Hasona57/Smart-Road/3D/led-3mm-green.snapshot.3/Renderings/led 3mm green.jpg

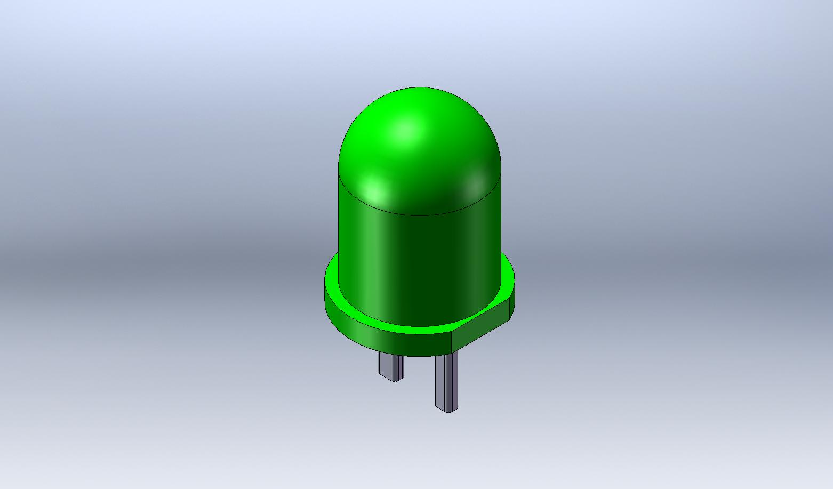
3D/led-3mm-green.snapshot.3/Renderings/led 3mm green.jpg
