Hasona57/Smart-Road/3D/led-3mm-green.snapshot.3/Renderings/untitled.340.jpg

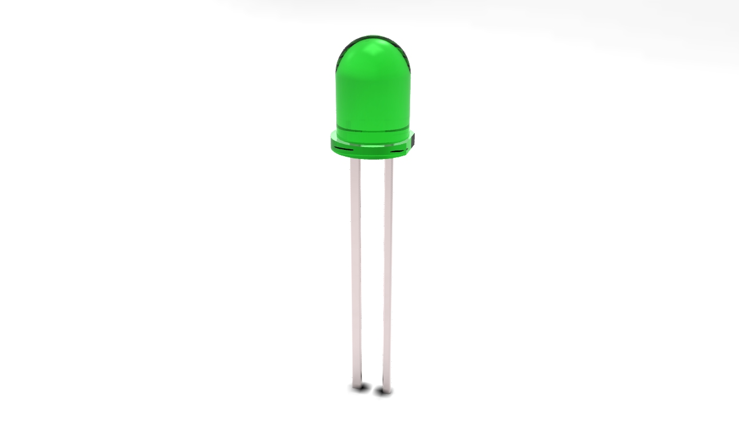
3D/led-3mm-green.snapshot.3/Renderings/untitled.340.jpg
