Hasona57/Smart-Road/3D/Traffic light module 3D/Traffic lights LED Module.jpg

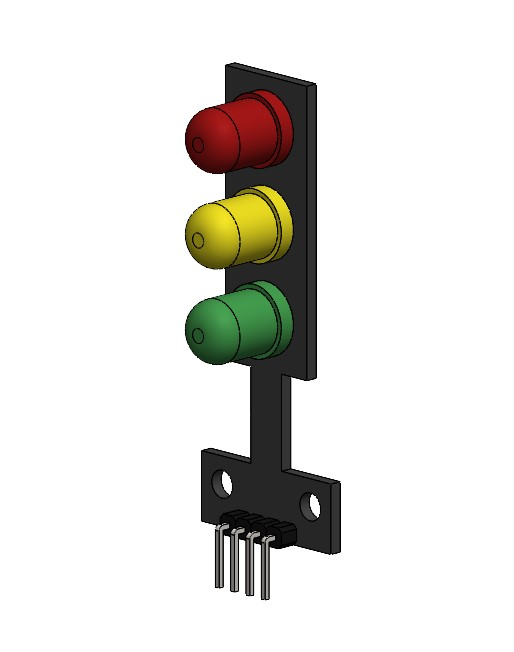
3D/Traffic light module 3D/Traffic lights LED Module.jpg
