Hasona57/Smart-Road/AI/assets/road3.jpg

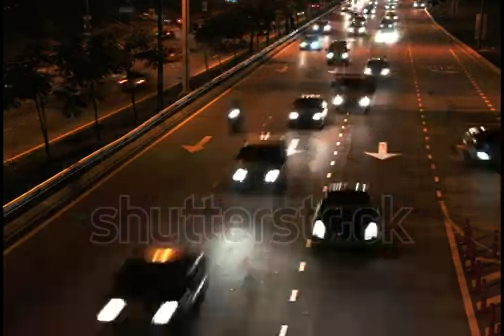
AI/assets/road3.jpg
