Hasona57/Smart-Road/AI/assets/road4.jpg

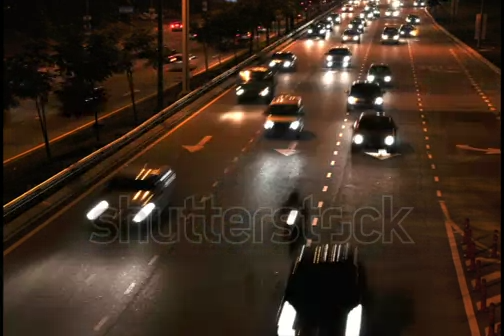
AI/assets/road4.jpg
