Hasona57/Smart-Road/AI/assets/road6.jpg

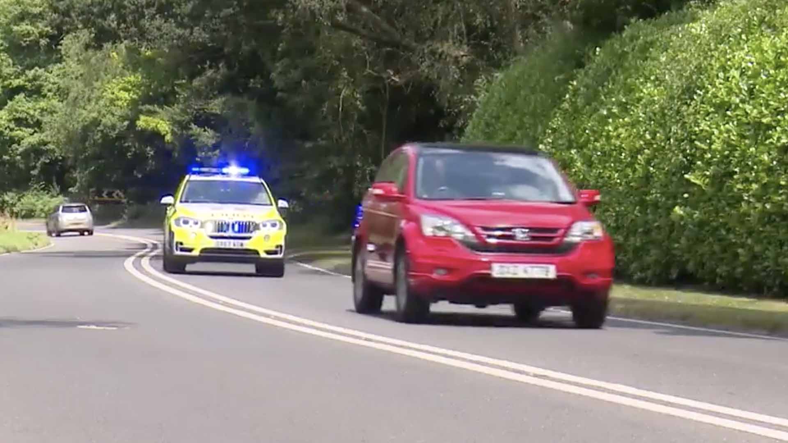
AI/assets/road6.jpg
