Hasona57/Smart-Road/AI/runs/detect/train/confusion_matrix.png

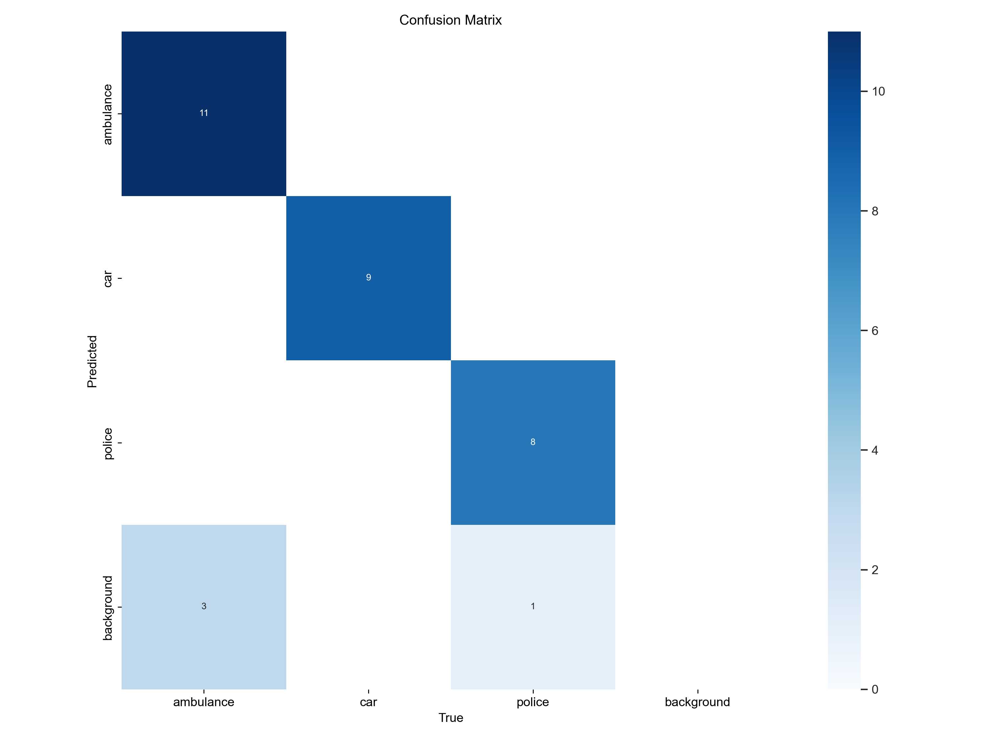
AI/runs/detect/train/confusion_matrix.png
