Hasona57/Smart-Road/AI/runs/detect/train/F1_curve.png

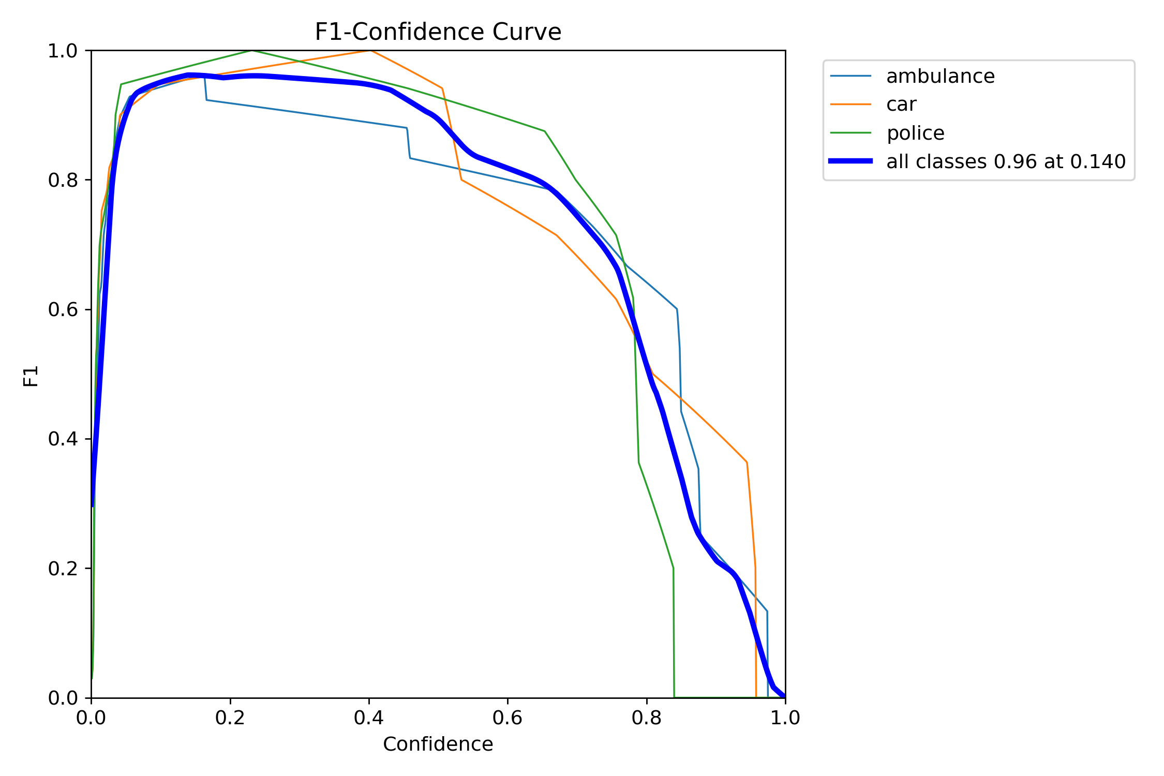
AI/runs/detect/train/F1_curve.png
