Hasona57/Smart-Road/AI/runs/detect/train/labels.jpg

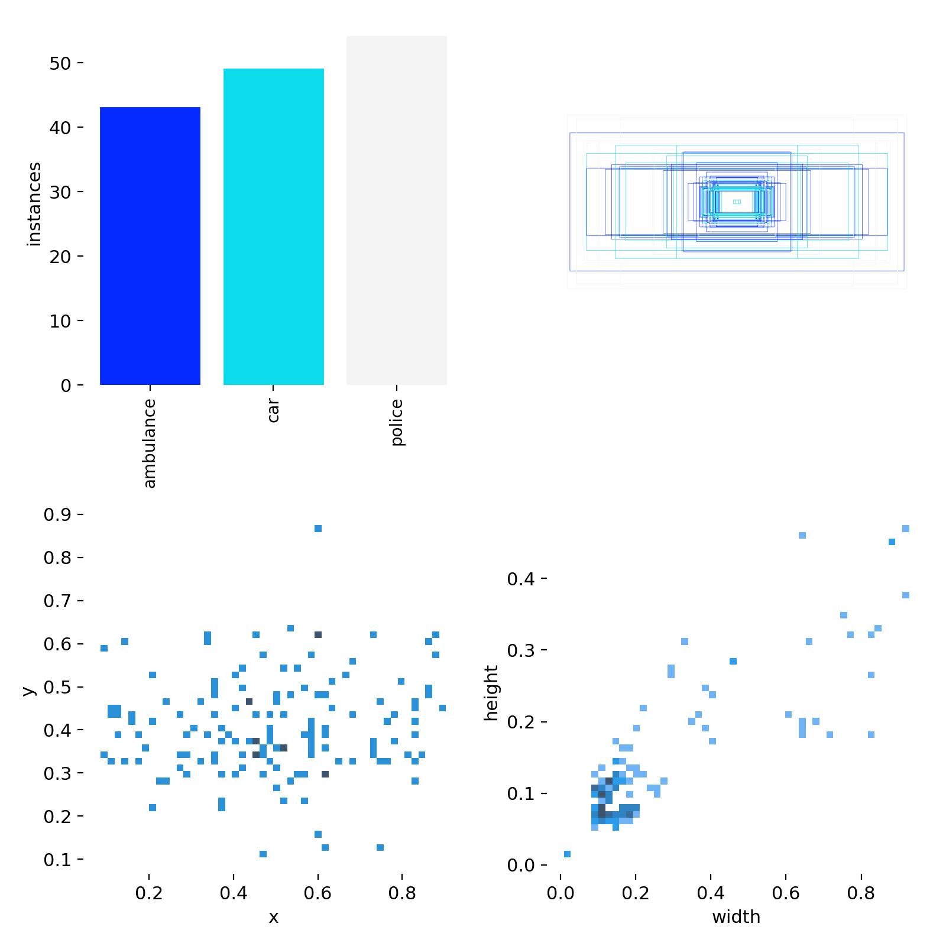
AI/runs/detect/train/labels.jpg
