Hasona57/Smart-Road/AI/runs/detect/train/labels_correlogram.jpg

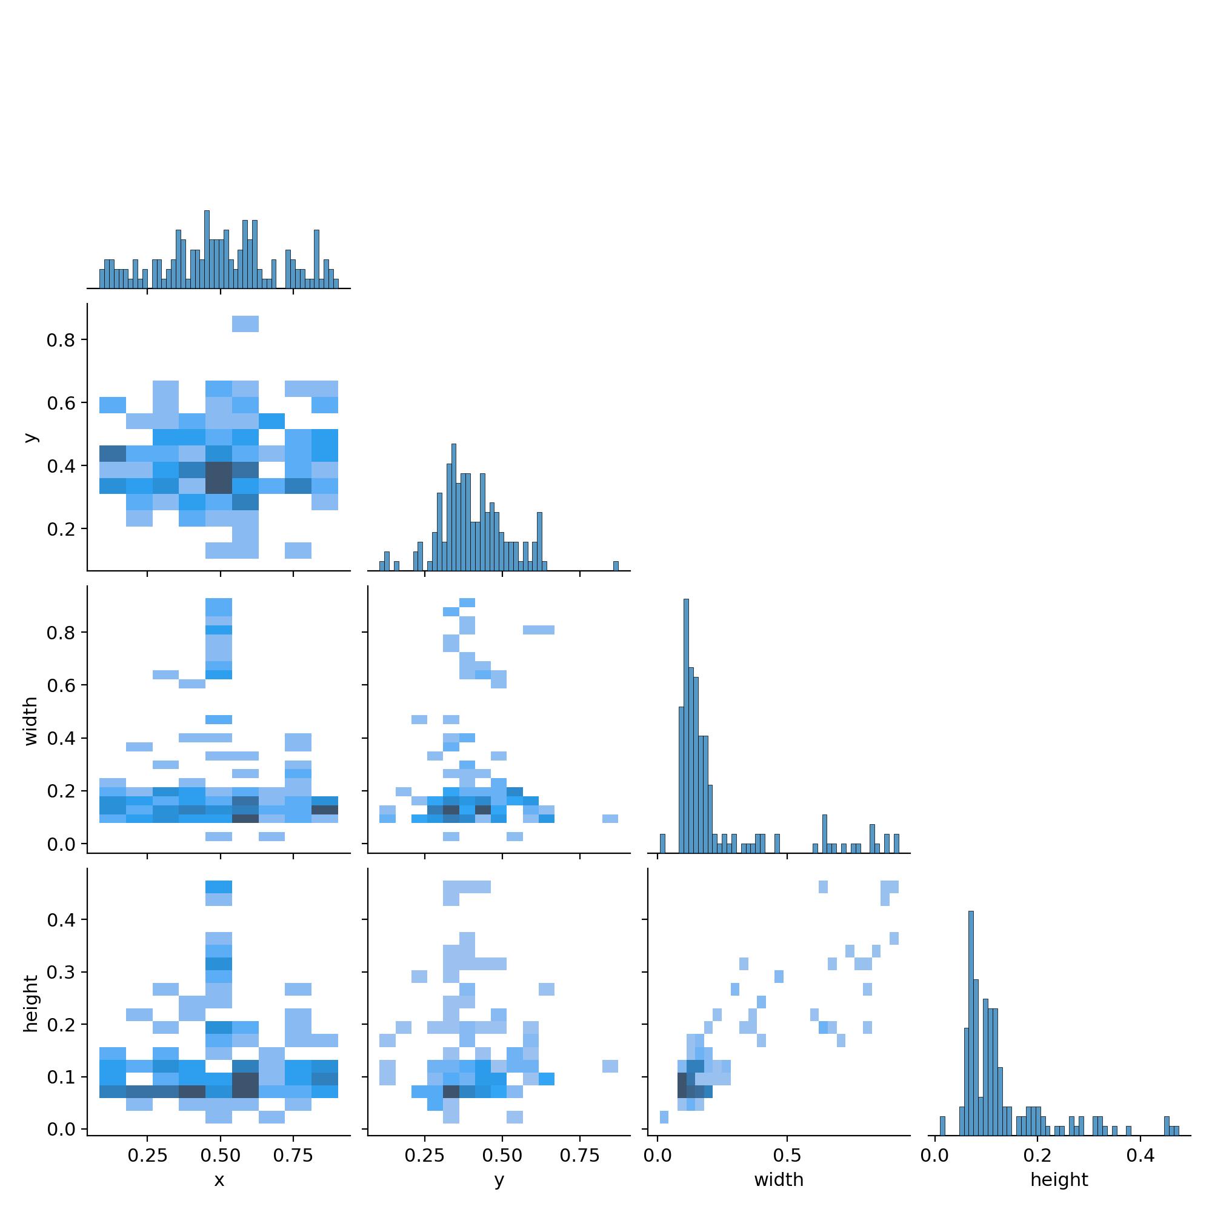
AI/runs/detect/train/labels_correlogram.jpg
