Hasona57/Smart-Road/AI/runs/detect/train/P_curve.png

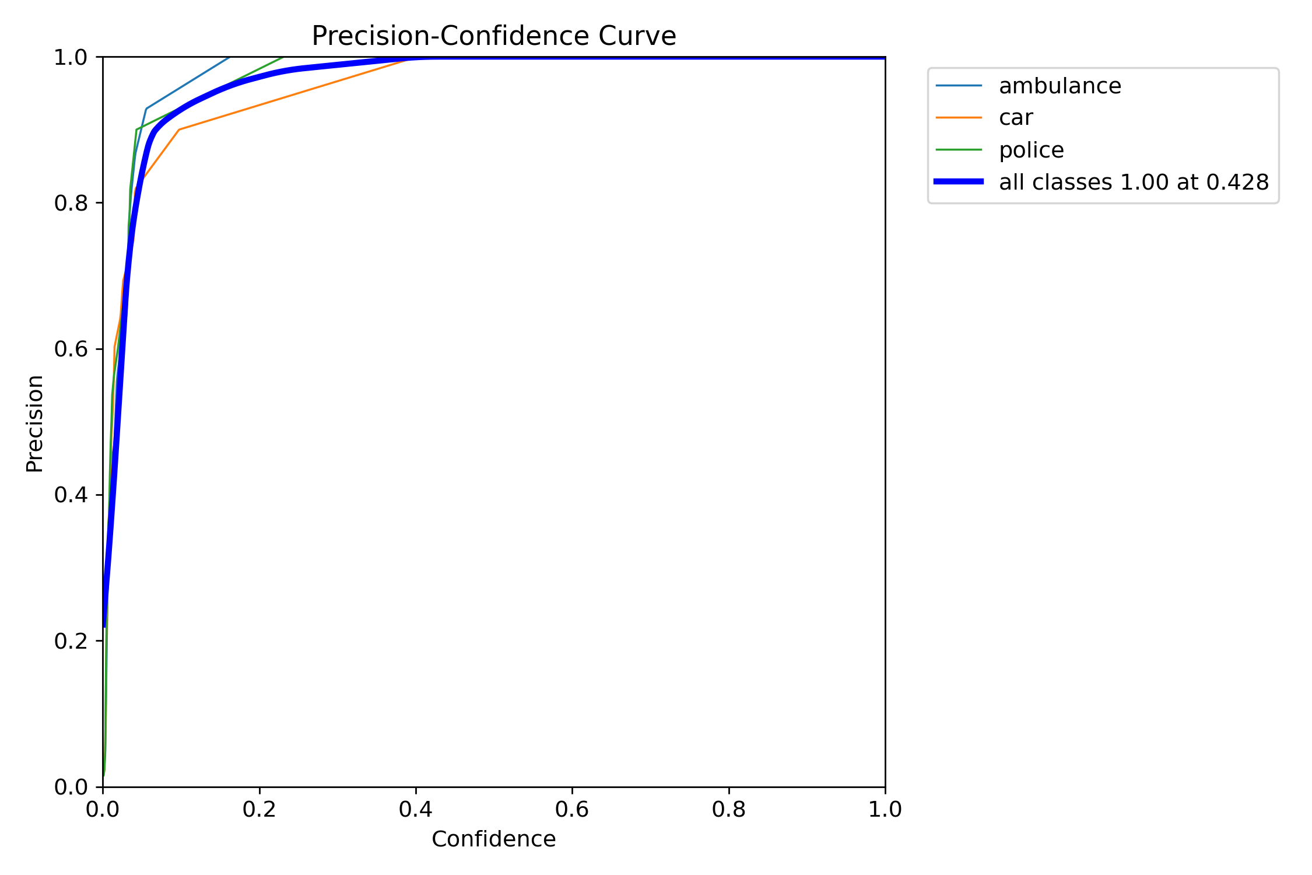
AI/runs/detect/train/P_curve.png
