Hasona57/Smart-Road/AI/runs/detect/train/PR_curve.png

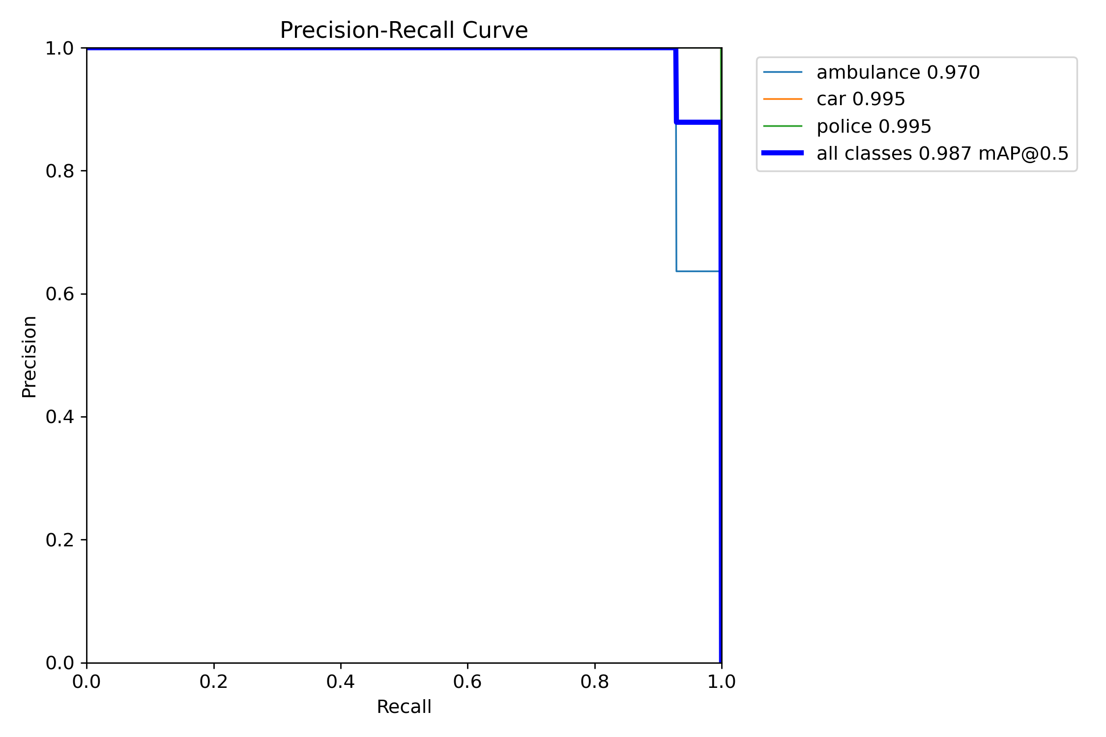
AI/runs/detect/train/PR_curve.png
