Hasona57/Smart-Road/AI/runs/detect/train/train_batch0.jpg

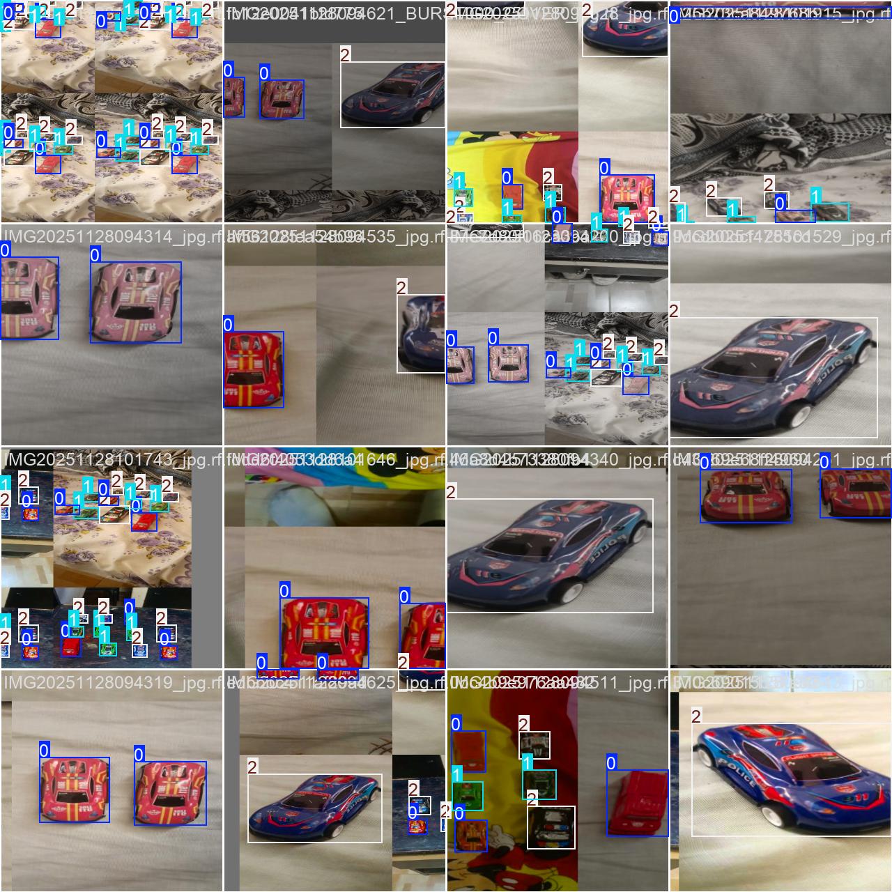
AI/runs/detect/train/train_batch0.jpg
