Hasona57/Smart-Road/AI/runs/detect/train/train_batch1.jpg

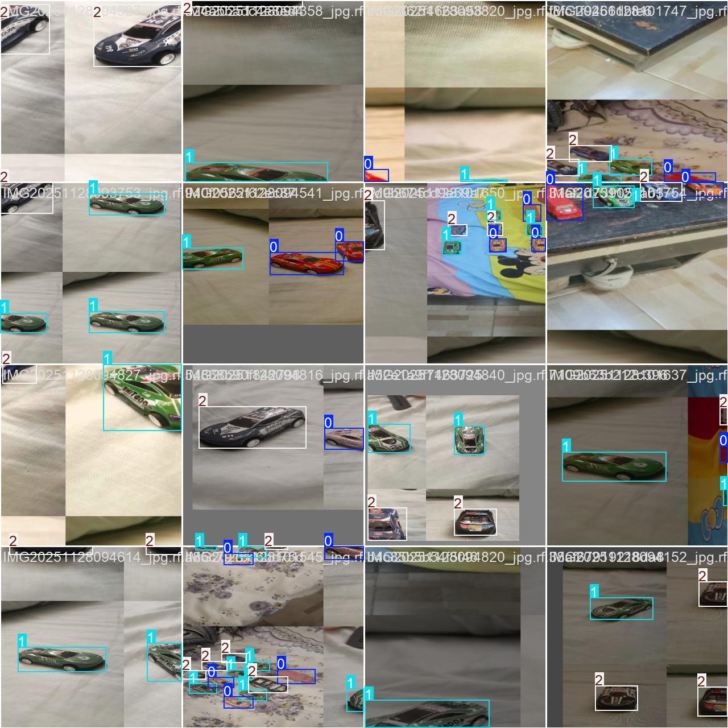
AI/runs/detect/train/train_batch1.jpg
