Hasona57/Smart-Road/AI/runs/detect/train/train_batch2.jpg

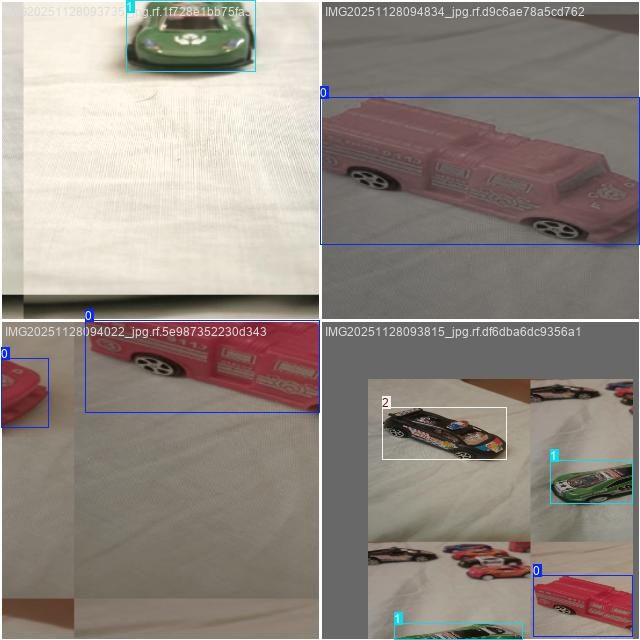
AI/runs/detect/train/train_batch2.jpg
