Hasona57/Smart-Road/AI/runs/detect/train/train_batch120.jpg

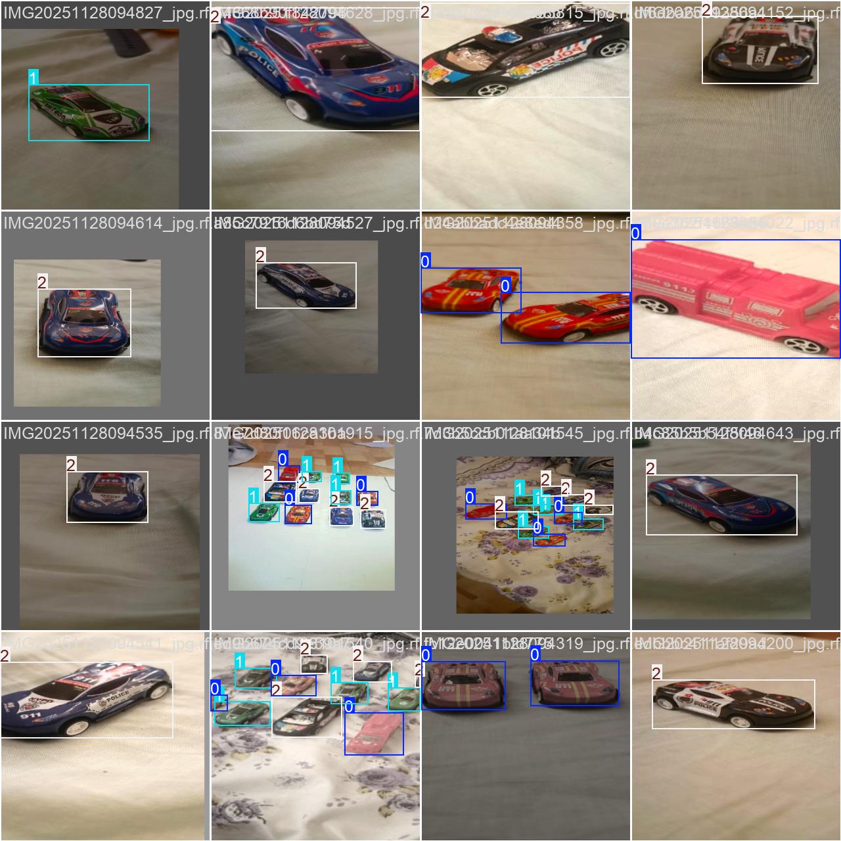
AI/runs/detect/train/train_batch120.jpg
