Hasona57/Smart-Road/AI/runs/detect/train/train_batch121.jpg

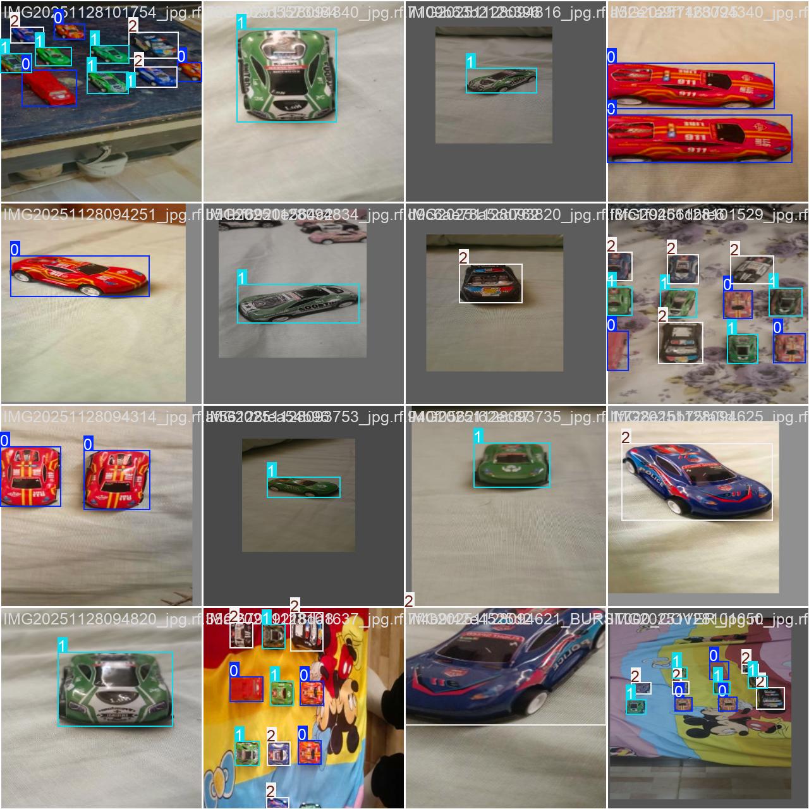
AI/runs/detect/train/train_batch121.jpg
