Hasona57/Smart-Road/AI/runs/detect/train/train_batch122.jpg

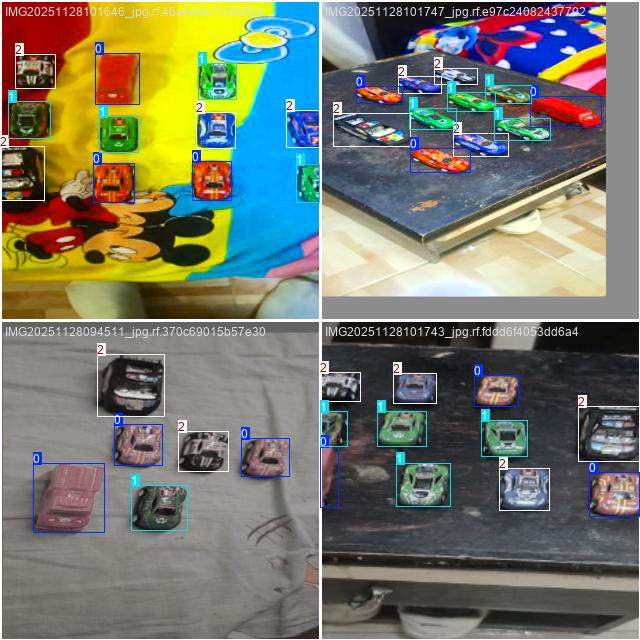
AI/runs/detect/train/train_batch122.jpg
