Hasona57/Smart-Road/AI/runs/detect/train/val_batch0_labels.jpg

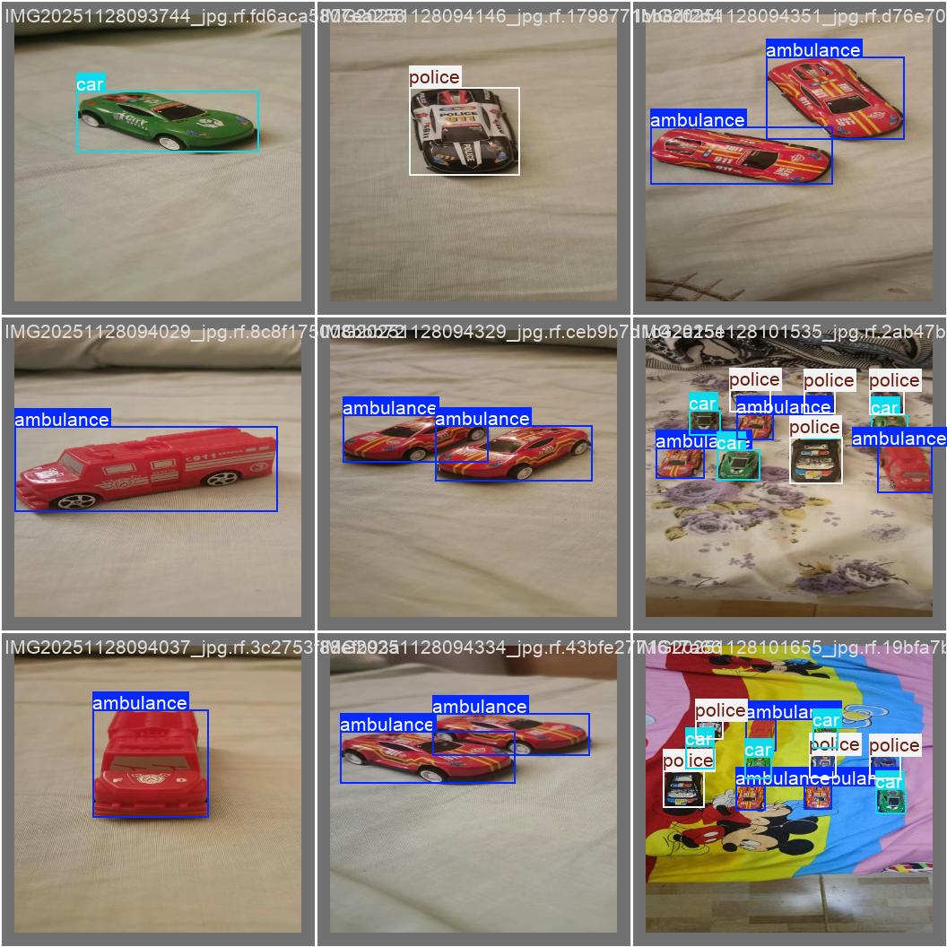
AI/runs/detect/train/val_batch0_labels.jpg
