Hasona57/Smart-Road/AI/runs/detect/train/val_batch0_pred.jpg

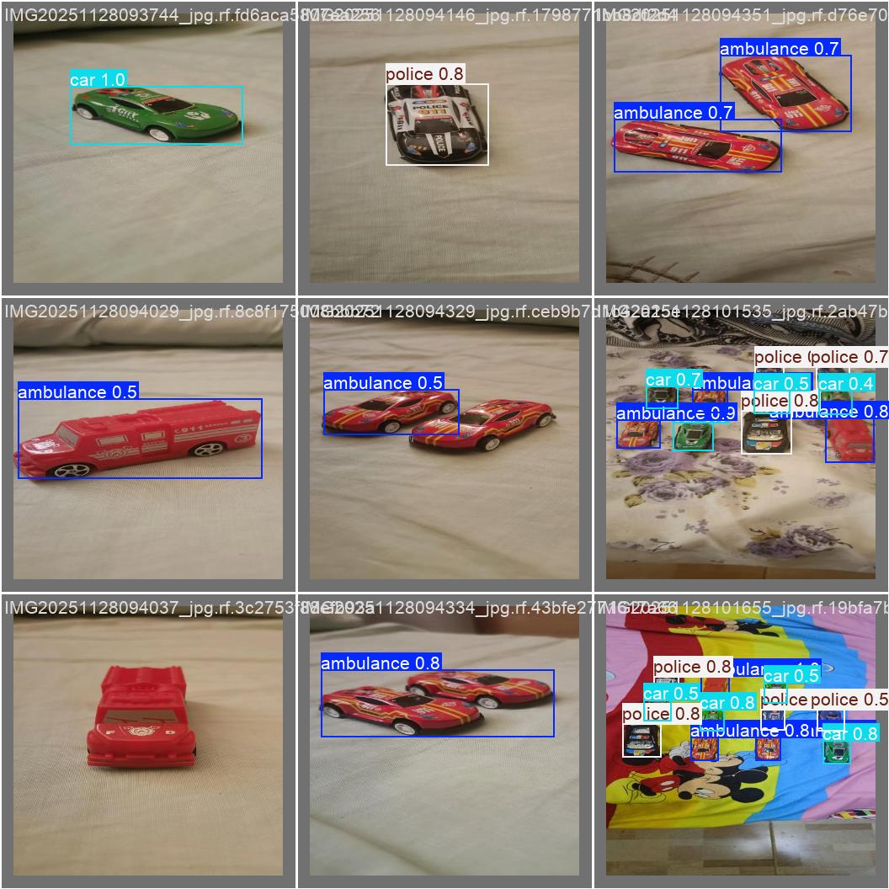
AI/runs/detect/train/val_batch0_pred.jpg
