Hasona57/Smart-Road/Code/Labels/Hassan/IMG20251128093744.jpg

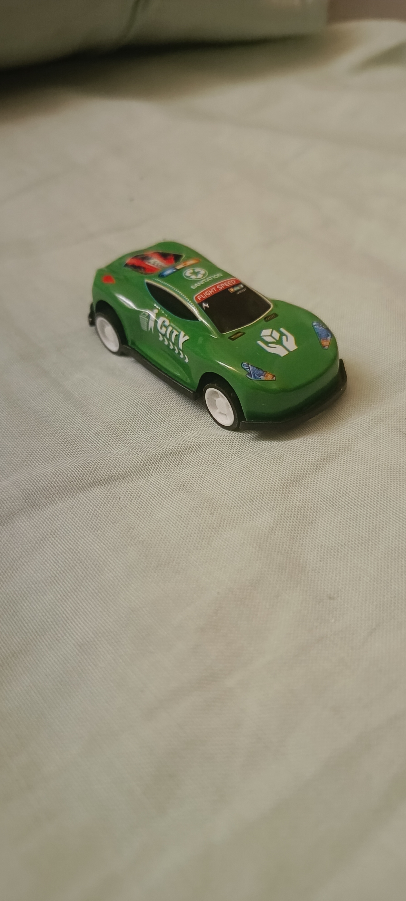
Code/Labels/Hassan/IMG20251128093744.jpg
