Hasona57/Smart-Road/Code/Labels/Hassan/IMG20251128093753.jpg

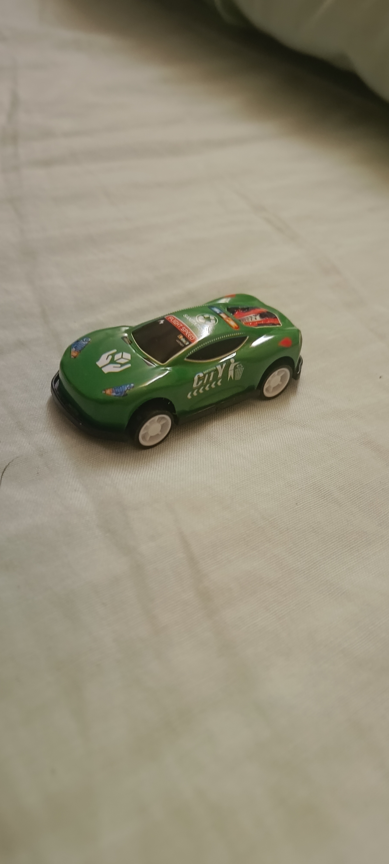
Code/Labels/Hassan/IMG20251128093753.jpg
