Hasona57/Smart-Road/Code/Labels/Hassan/IMG20251128093759.jpg

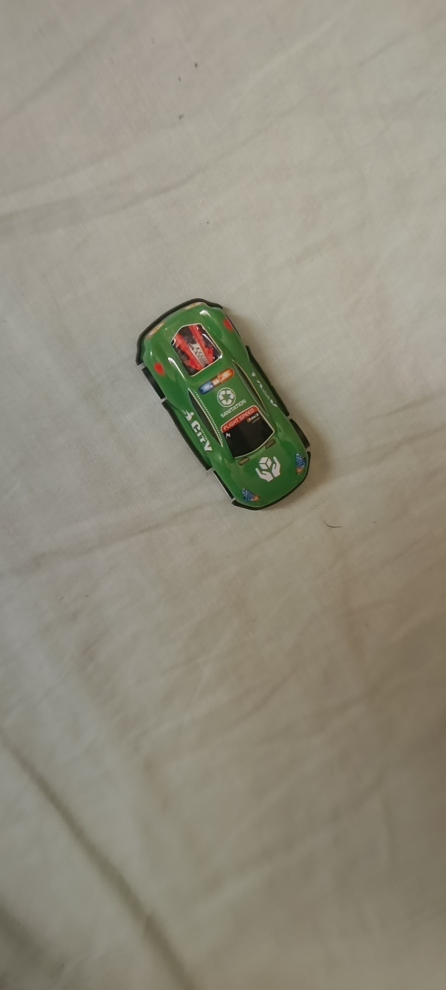
Code/Labels/Hassan/IMG20251128093759.jpg
