Hasona57/Smart-Road/Code/Labels/Hassan/IMG20251128093808.jpg

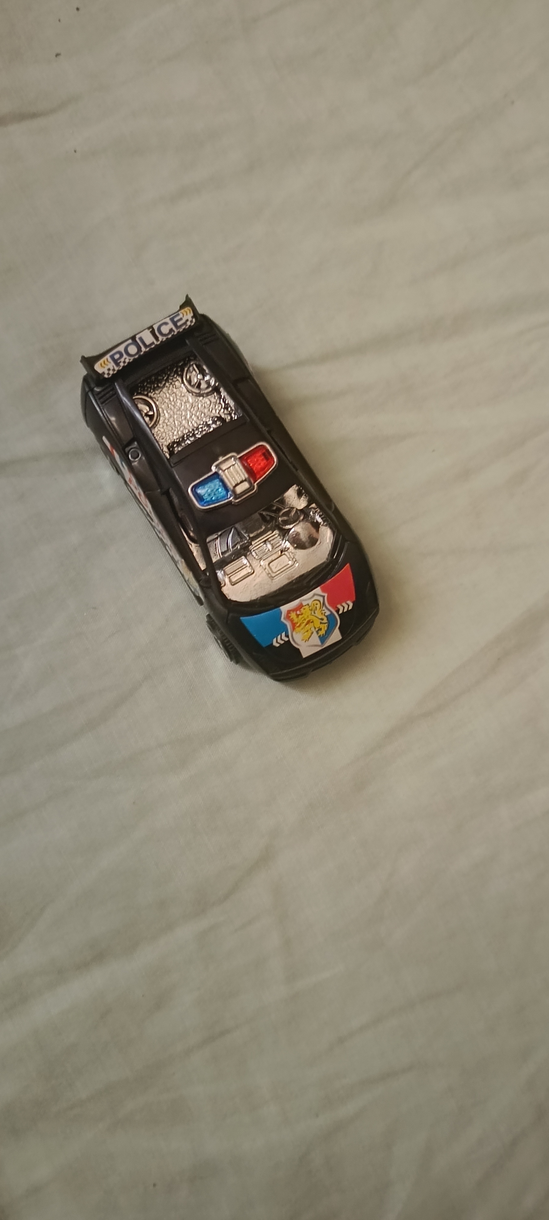
Code/Labels/Hassan/IMG20251128093808.jpg
