Hasona57/Smart-Road/Code/Labels/Hassan/IMG20251128093820.jpg

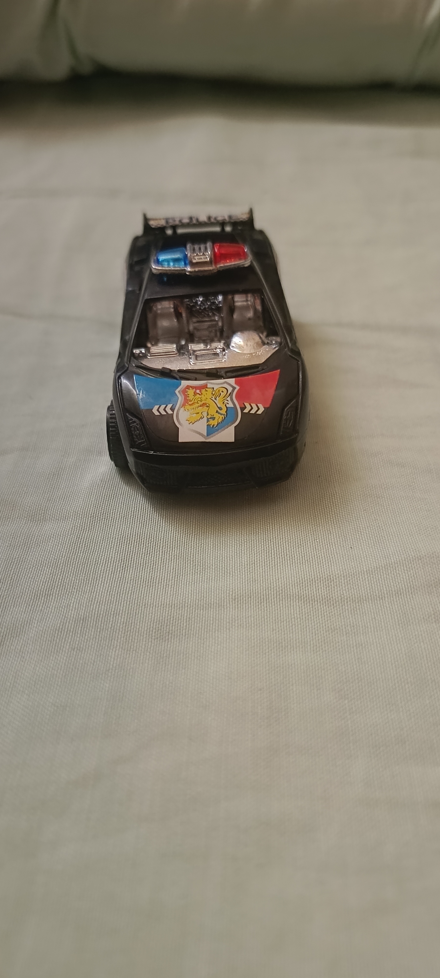
Code/Labels/Hassan/IMG20251128093820.jpg
