Hasona57/Smart-Road/Code/Labels/Hassan/IMG20251128093831.jpg

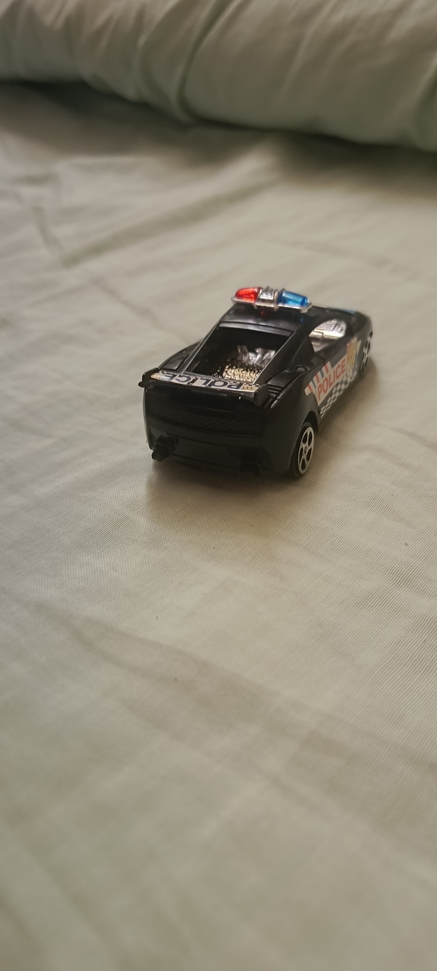
Code/Labels/Hassan/IMG20251128093831.jpg
