Hasona57/Smart-Road/Code/Labels/Hassan/IMG20251128094015.jpg

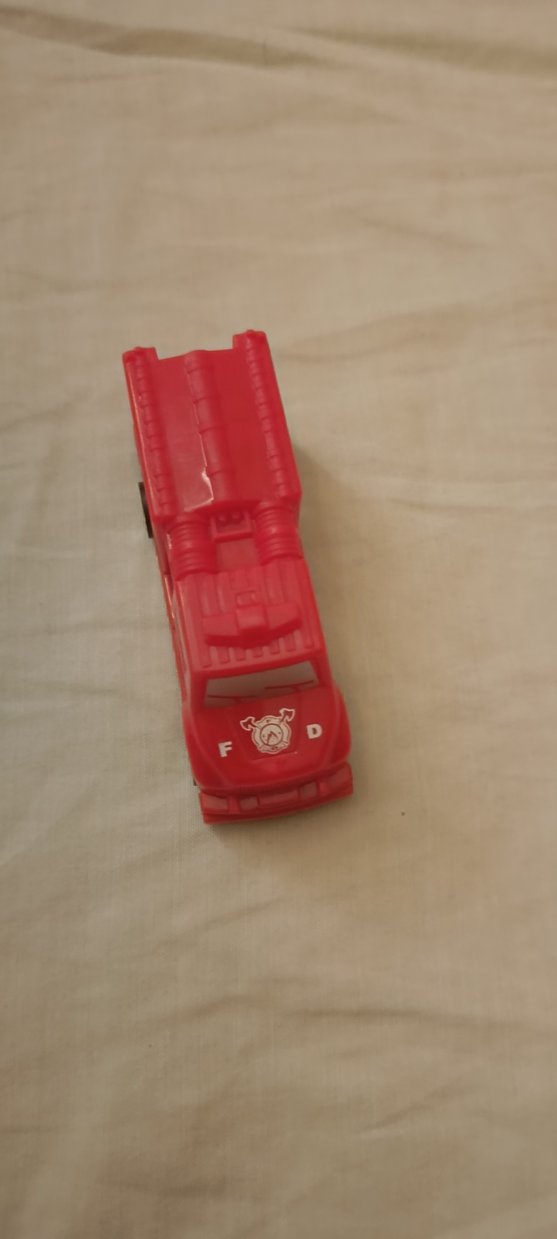
Code/Labels/Hassan/IMG20251128094015.jpg
