Hasona57/Smart-Road/Code/Labels/Hassan/IMG20251128094037.jpg

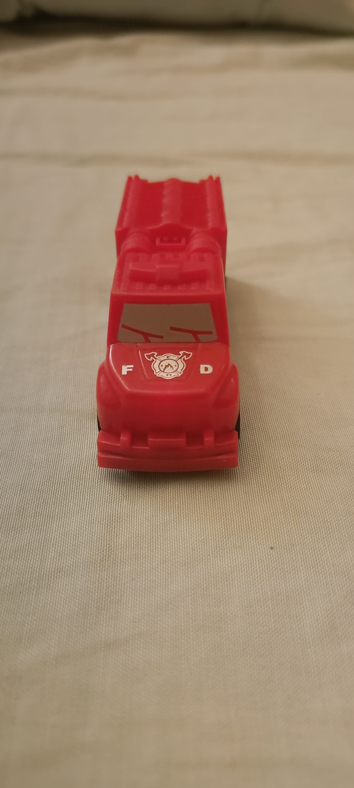
Code/Labels/Hassan/IMG20251128094037.jpg
