Hasona57/Smart-Road/Code/Labels/Hassan/IMG20251128094051.jpg

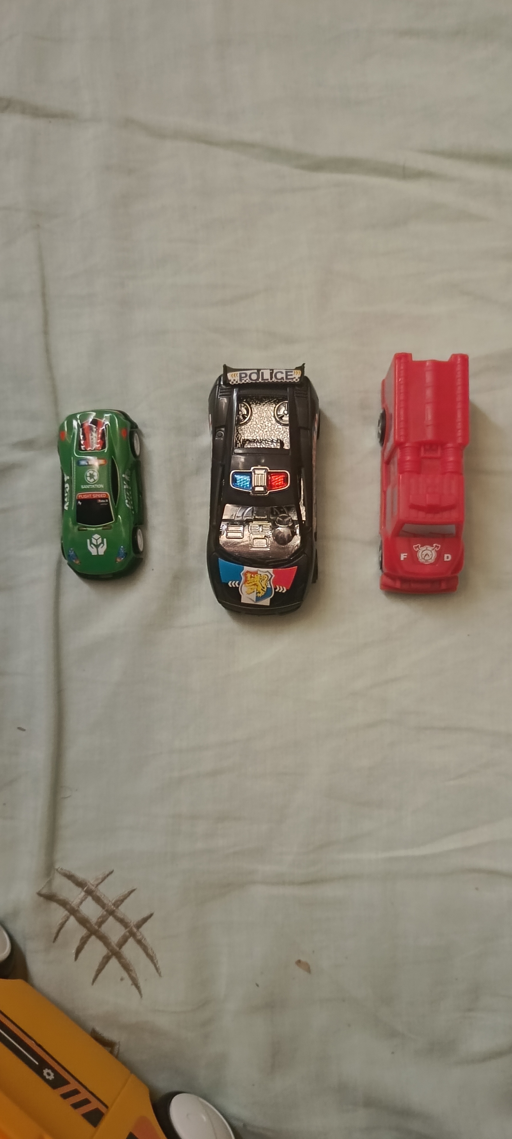
Code/Labels/Hassan/IMG20251128094051.jpg
