Hasona57/Smart-Road/Code/Labels/Hassan/IMG20251128094816.jpg

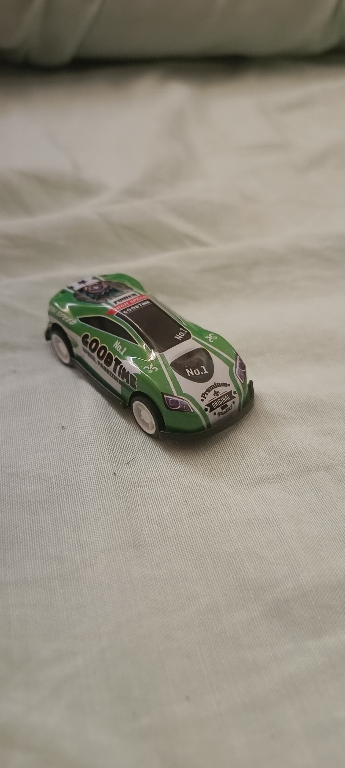
Code/Labels/Hassan/IMG20251128094816.jpg
