Hasona57/Smart-Road/Code/Labels/IMG_20251128_135731.jpg

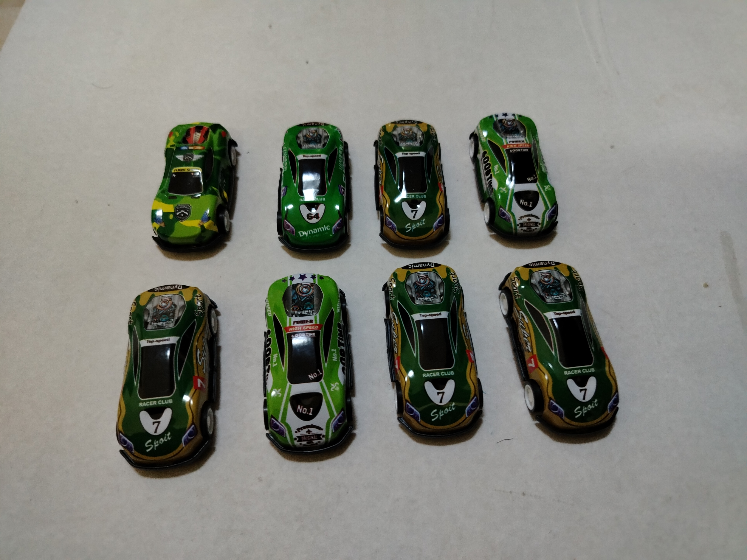
Code/Labels/IMG_20251128_135731.jpg
