Hasona57/Smart-Road/Code/Labels/IMG_20251128_140136.jpg

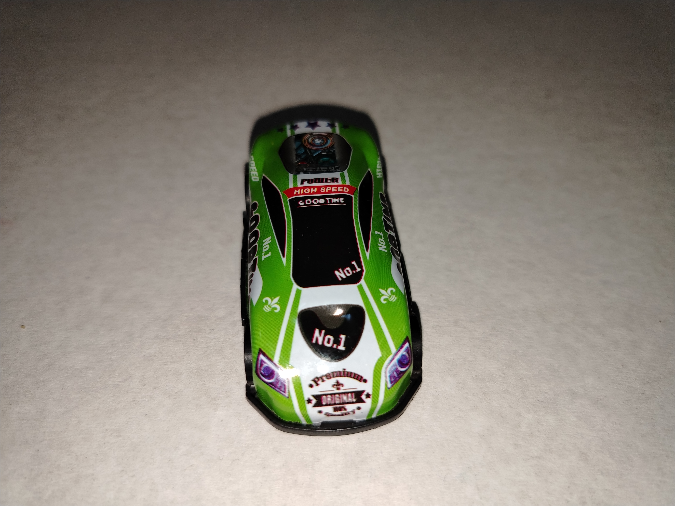
Code/Labels/IMG_20251128_140136.jpg
