Hasona57/Smart-Road/Code/Labels/IMG_20251128_140236.jpg

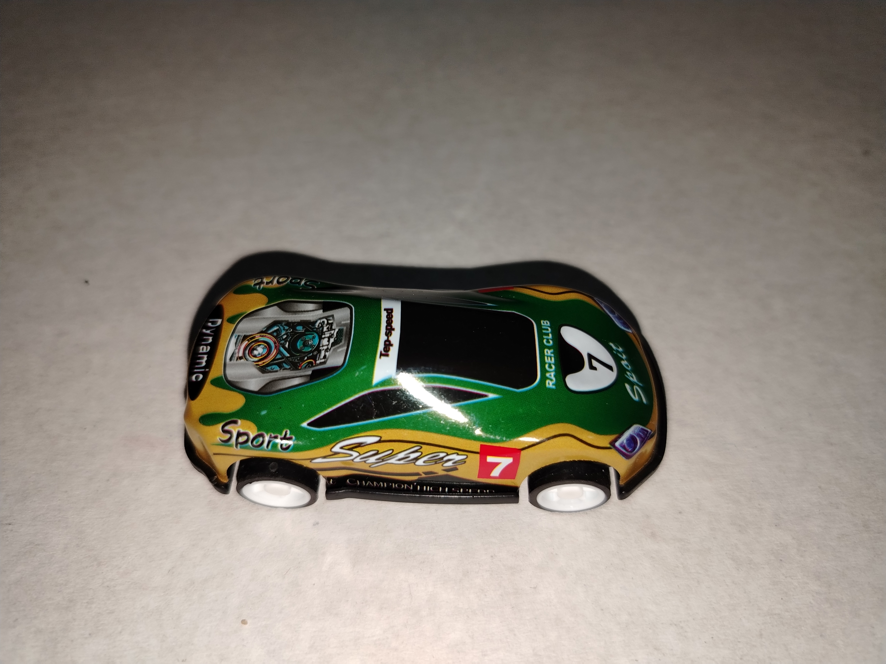
Code/Labels/IMG_20251128_140236.jpg
