Hasona57/Smart-Road/Code/Labels/IMG_20251201_071935.jpg

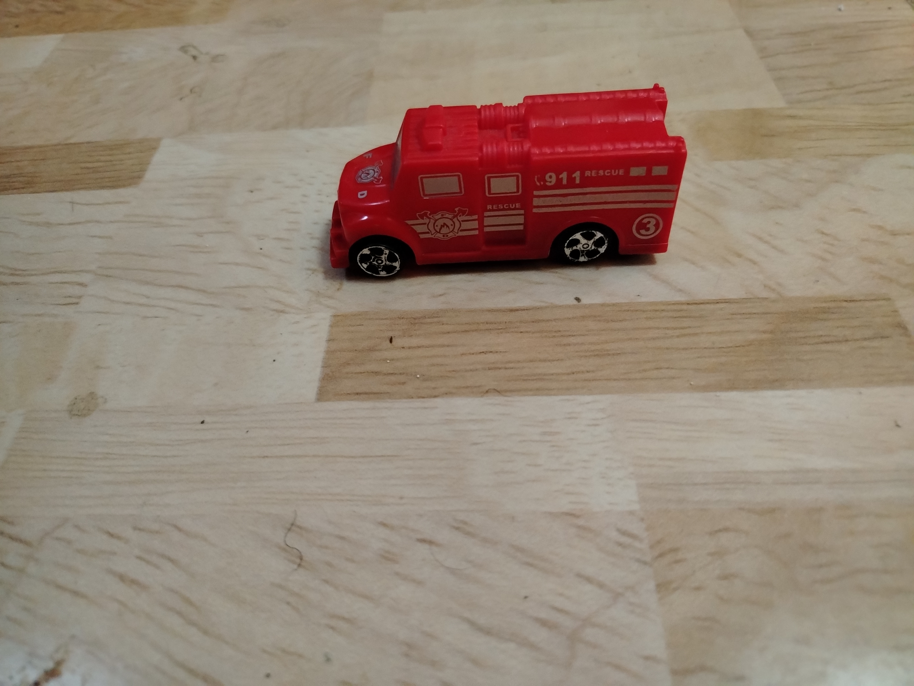
Code/Labels/IMG_20251201_071935.jpg
