Hasona57/Smart-Road/Code/Labels/IMG_20251201_072016.jpg

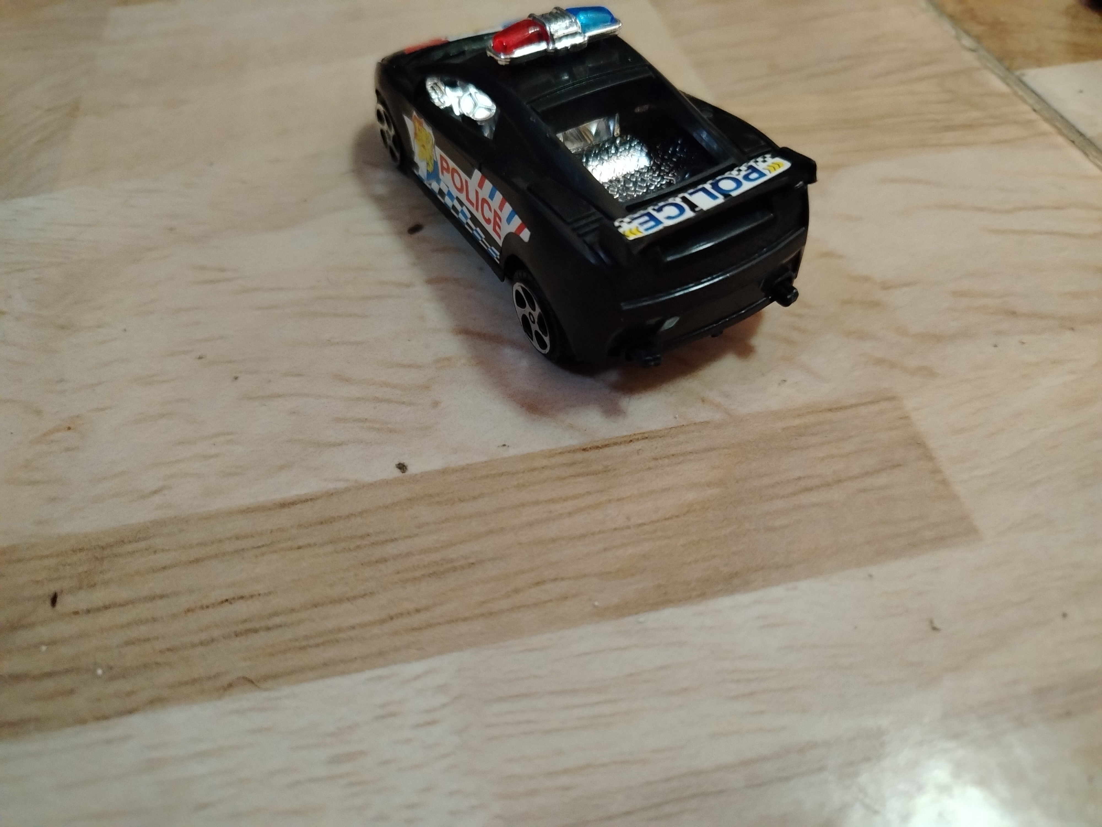
Code/Labels/IMG_20251201_072016.jpg
