Hasona57/Smart-Road/Images/830-Tie-Point-Breadboard.jpg

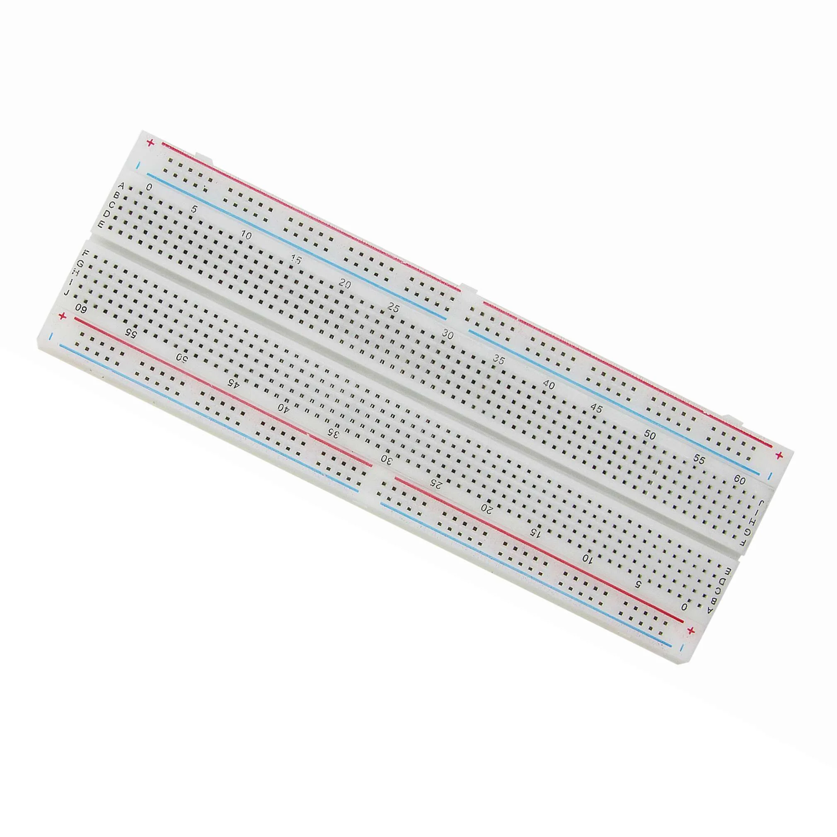
Images/830-Tie-Point-Breadboard.jpg
