Hasona57/Smart-Road/Images/17160e21-c3e8-4156-8168-b5e637ebaf46.jpg

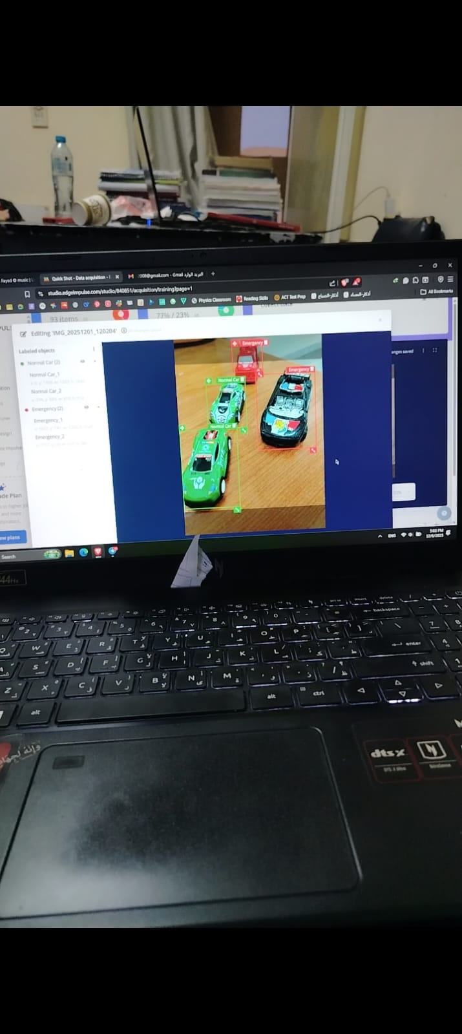
Images/17160e21-c3e8-4156-8168-b5e637ebaf46.jpg
