Hasona57/Smart-Road/Images/Adapter.jpg

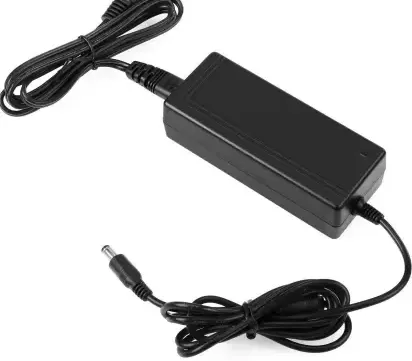
Images/Adapter.jpg
