Hasona57/Smart-Road/Images/Male-to-Female-Jumper-Wire.jpg

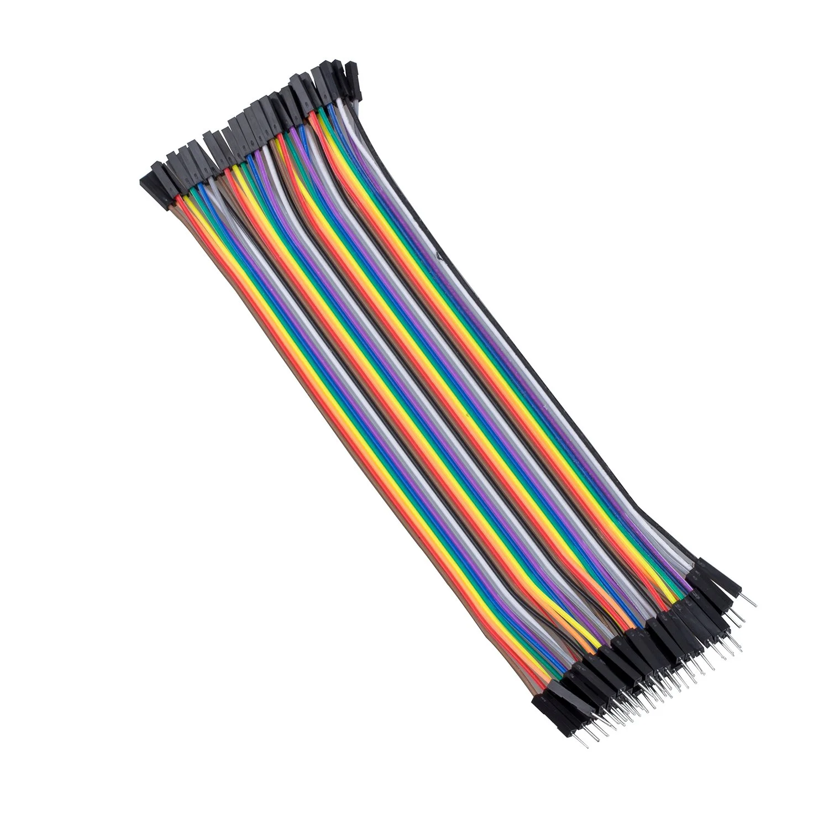
Images/Male-to-Female-Jumper-Wire.jpg
