Hasona57/Smart-Road/Images/Relay-Module.jpg

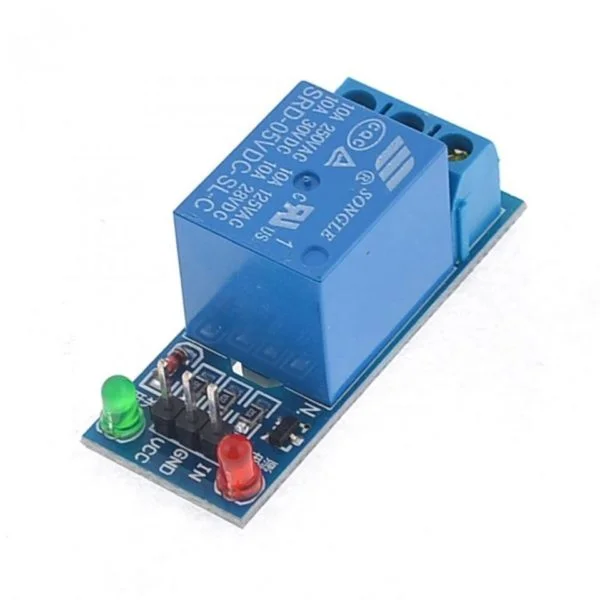
Images/Relay-Module.jpg
