Hasona57/Smart-Road/Images/Resistor220ohm0.25W.jpg

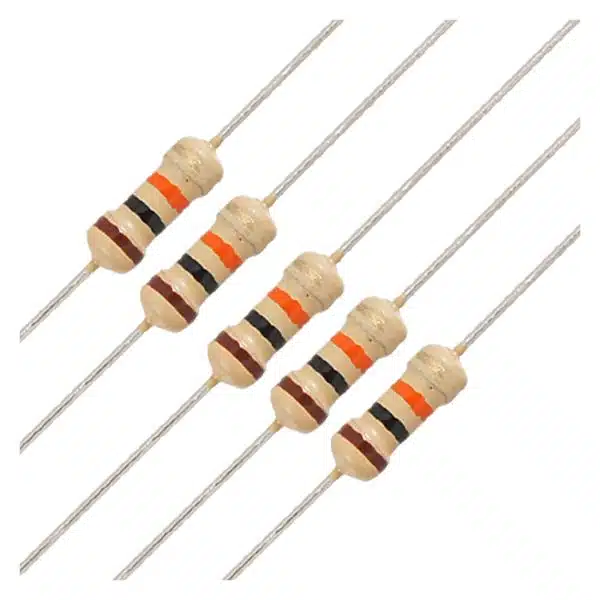
Images/Resistor220ohm0.25W.jpg
