Hasona57/Smart-Road/Images/TypeCtoSDcard.jpg

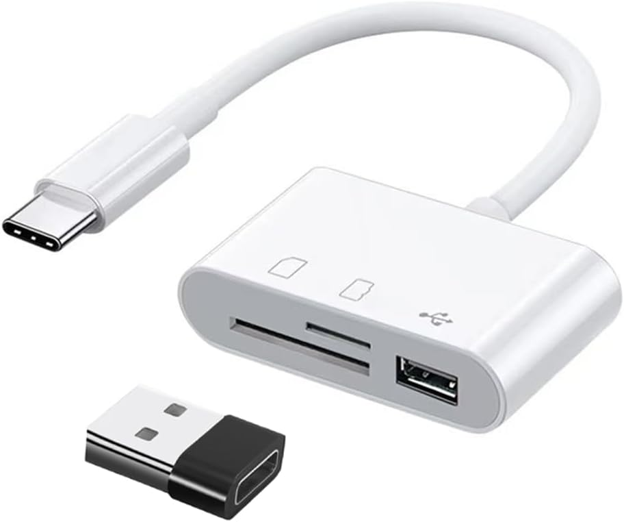
Images/TypeCtoSDcard.jpg
