Hasona57/Smart-Road/AI/runs/detect/train/results.png

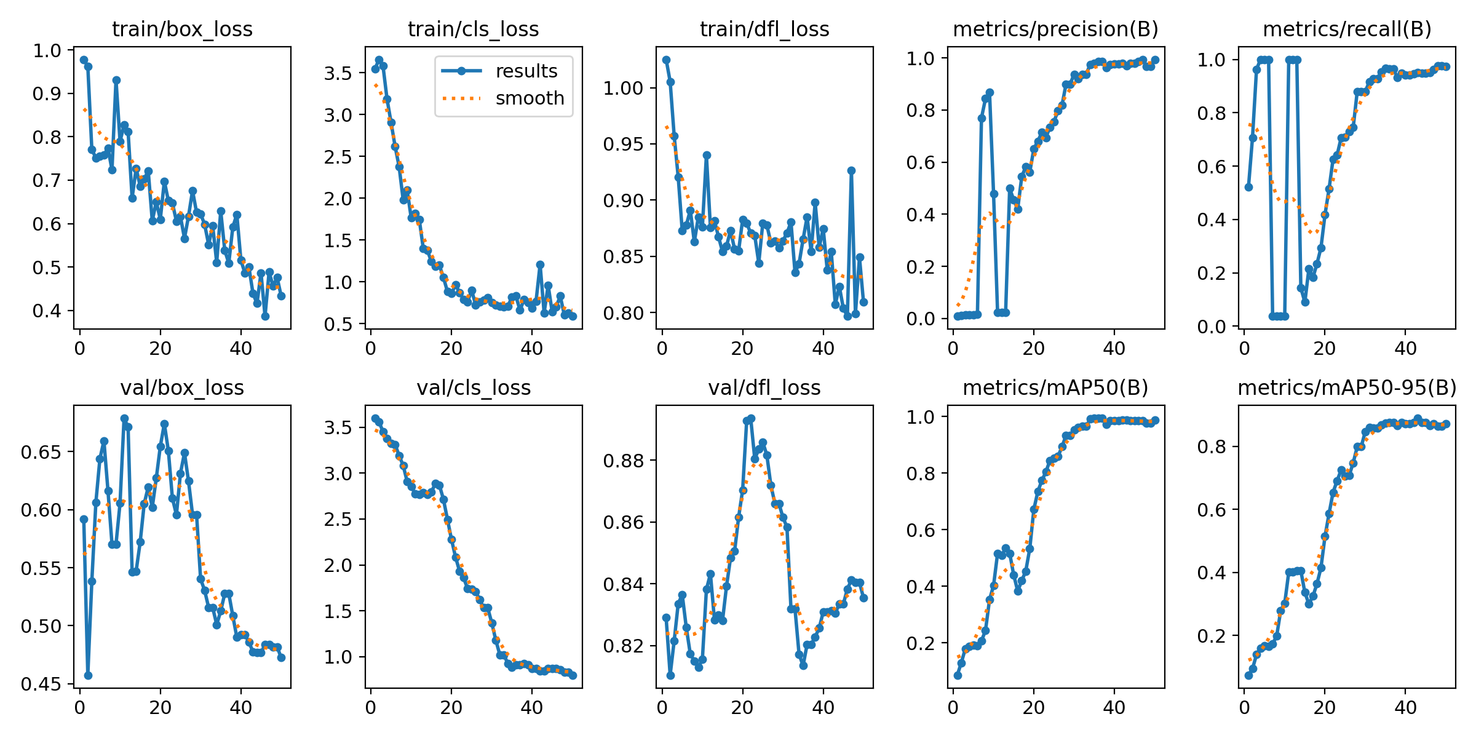
AI/runs/detect/train/results.png
